MOSH-Insa-Toulouse/2022-2023-4GP-Thang-Tien/ProjetCapteur_kicad/Models/pin_header/14-Pin Header - Female - 2.54mm.step

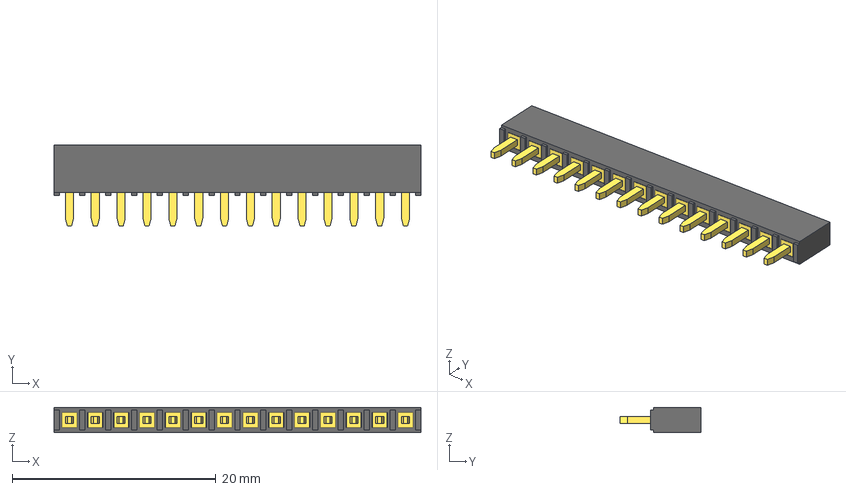
[picture p31: CAD file, 2023-05-17]
ProjetCapteur_kicad/Models/pin_header/14-Pin Header - Female - 2.54mm.step
36.1 x 8.00 x 2.50 mm
