MOSH-Insa-Toulouse/2022-2023-4GP-Thang-Tien/ProjetCapteur_kicad/Models/pin_header/11-Pin Header - Female - 2.54mm.step

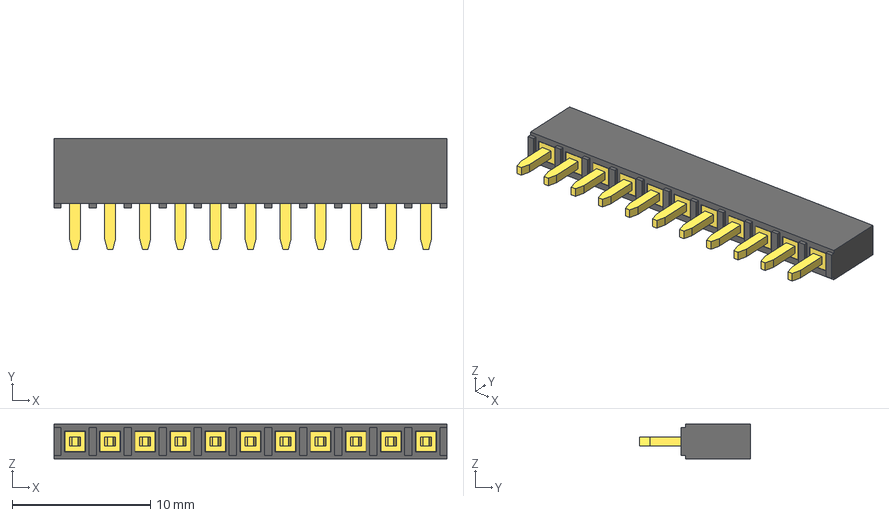
[picture p38: CAD file, 2023-05-17]
ProjetCapteur_kicad/Models/pin_header/11-Pin Header - Female - 2.54mm.step
28.4 x 8.00 x 2.50 mm
